CodeR-na-r1/TriangleNodesARGB/src/SerialBus/tests/for 2 boards/Node.ino

// slave

#define DEBUG_

#include "SerialBusSlave.h"

SerialBusSlave bus(4, 0, 16, 13, 50);  // RX 2 TX 3 Fake 0

void setup() {
  Serial.begin(9600);
}

bool flag = false;
char s[15] = { '1', '3', '-', 's', 'u', 'p', 'e', 'r', 'S', 't', 'r', 'i', 'n', 'g', '!' };

void loop() {
  if (!flag) {

    getData();  // data from test 2

    Serial.println("getData 1 completed");

    bus.send(1, s, 15);  // send for getData address == 13

    Serial.println("send completed");

    getData();  // data from test 3 (broadcast)

    flag = true;
  }
}

void getData() {

  while (!bus.available()) {
    delay(1);
  }

  bus.getData()[bus.getSizeData()] = '\0';
  Serial.println(String((const char *)bus.getData()));
  Serial.print("Adress from = ");
  Serial.println(String(bus.getTXaddress()));
}
